ddanijell/ATU-Antenna-Tuner-System/Photo/ATU130_and_ATUdisplay.jpg

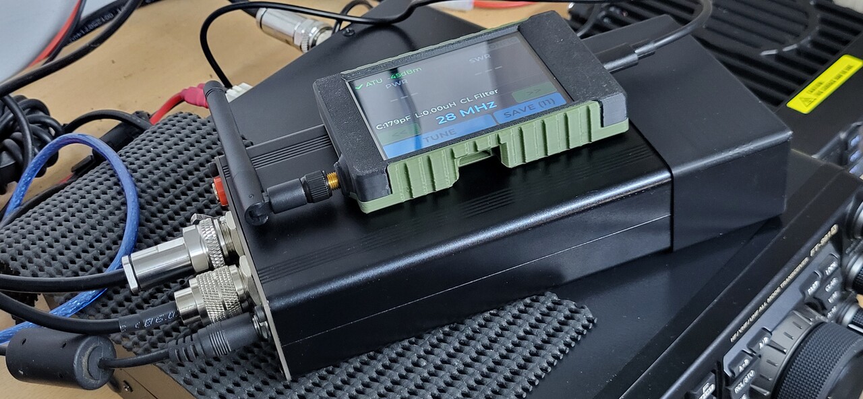
Photo/ATU130_and_ATUdisplay.jpg
