ddanijell/ATU-Antenna-Tuner-System/Photo/ATU130_front_cover.jpg

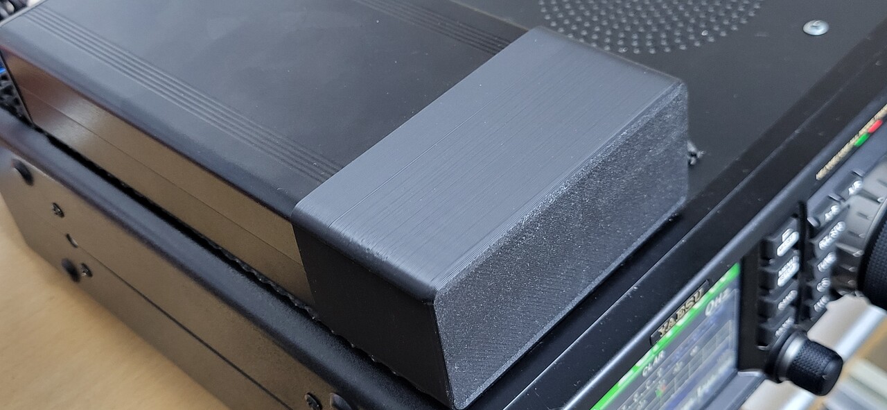
Photo/ATU130_front_cover.jpg
