ddanijell/ATU-Antenna-Tuner-System/Photo/ATU_transiver.jpg

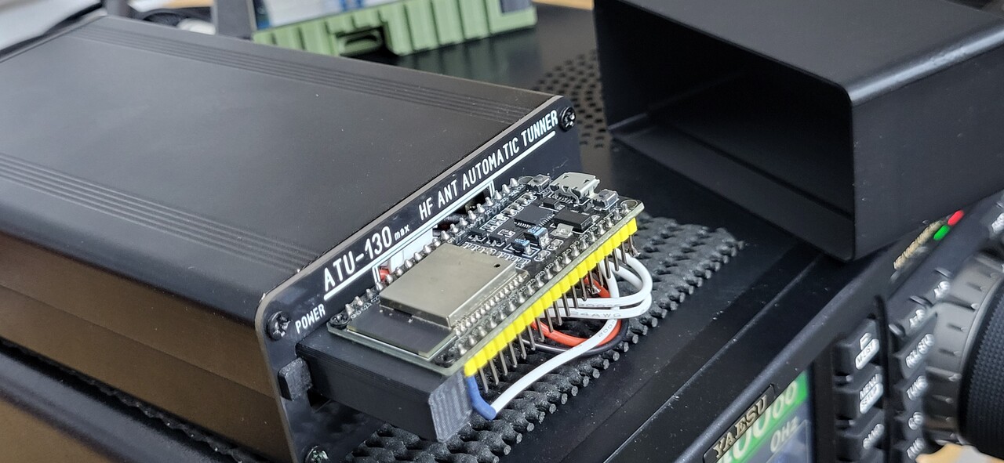
Photo/ATU_transiver.jpg
