ddanijell/ATU-Antenna-Tuner-System/Photo/ATUdisplay_back.jpg

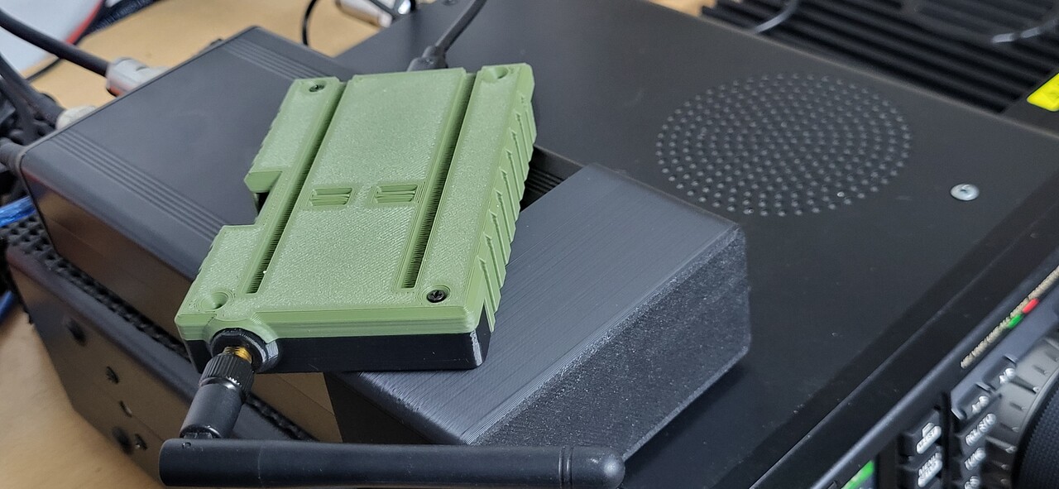
Photo/ATUdisplay_back.jpg
