ddanijell/ATU-Antenna-Tuner-System/Photo/Brightnes_Pair.jpg

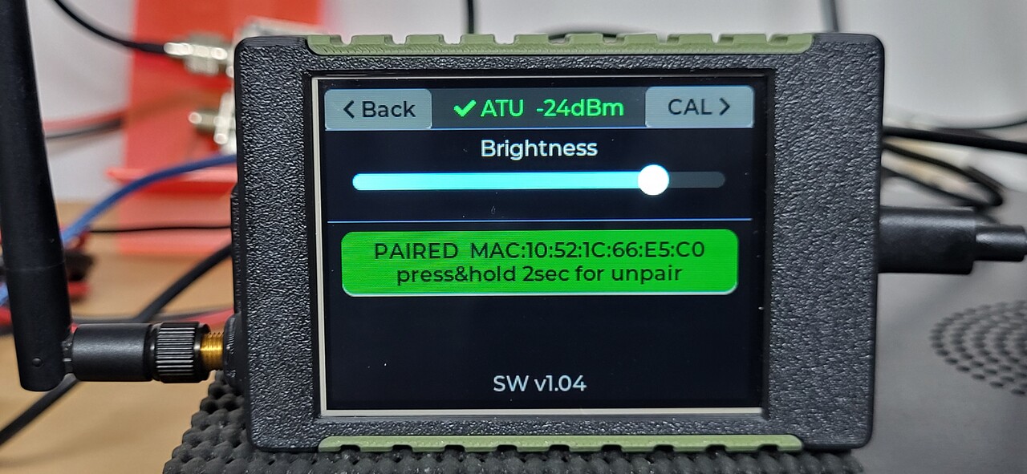
Photo/Brightnes_Pair.jpg
