ddanijell/ATU-Antenna-Tuner-System/Photo/CYD_ESP32_PCB.jpg

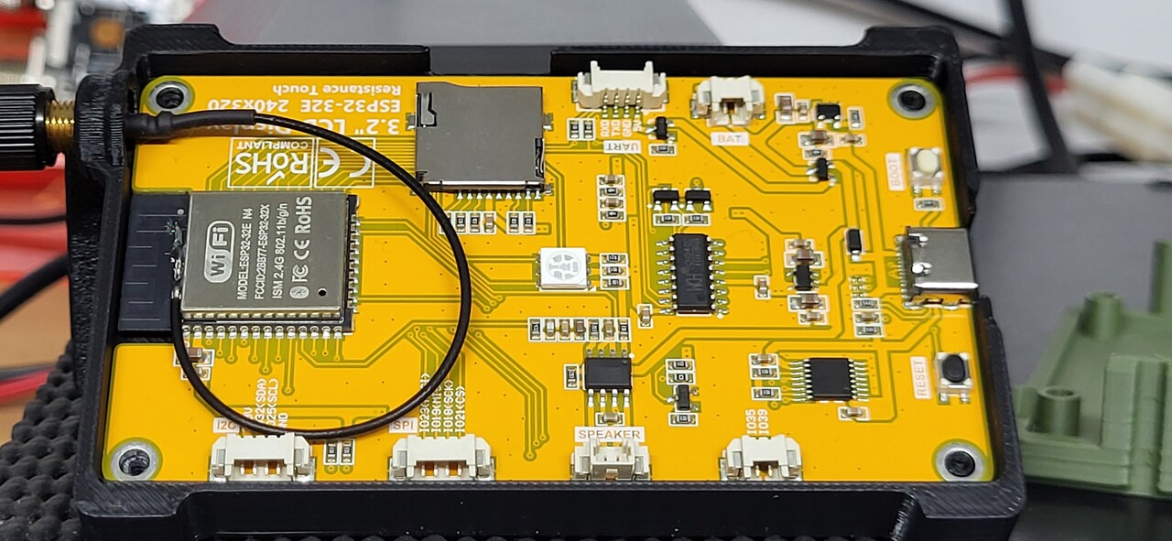
Photo/CYD_ESP32_PCB.jpg
