ddanijell/ATU-Antenna-Tuner-System/Photo/inside_atu130.jpg

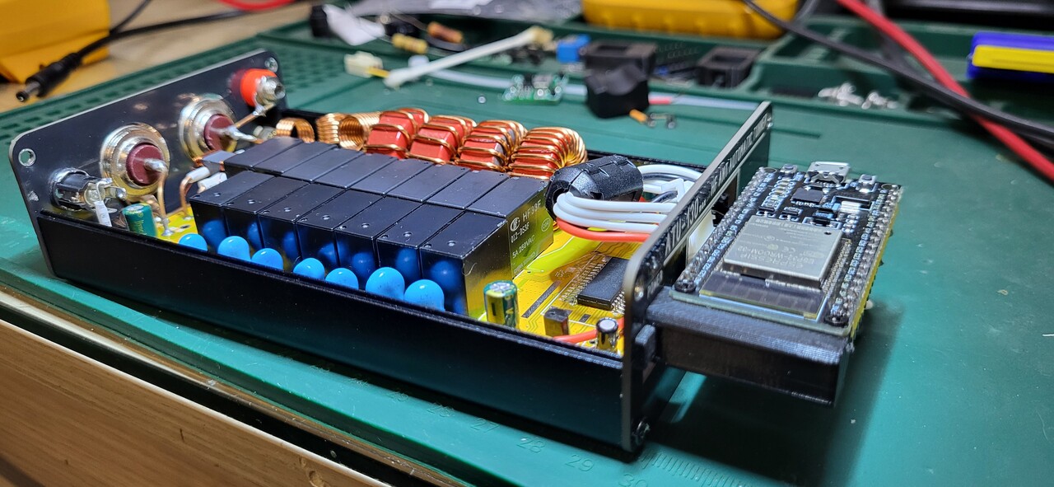
Photo/inside_atu130.jpg
