ddanijell/ATU-Antenna-Tuner-System/Photo/sideview.jpg

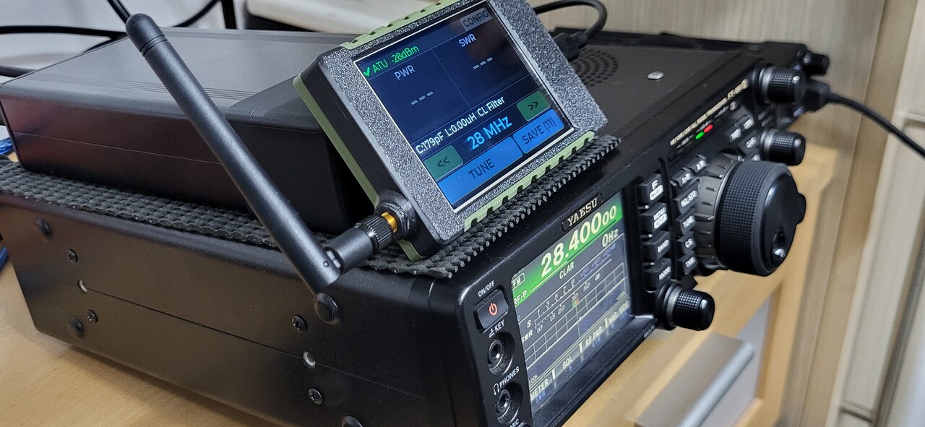
Photo/sideview.jpg
