ddanijell/ATU-Antenna-Tuner-System/Photo/system_01.jpg

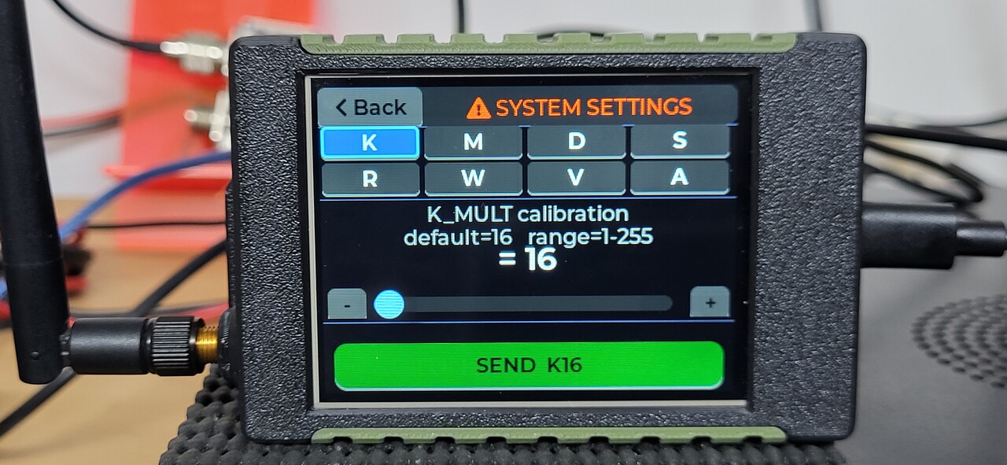
Photo/system_01.jpg
