ddanijell/ATU-Antenna-Tuner-System/Photo/system_06.jpg

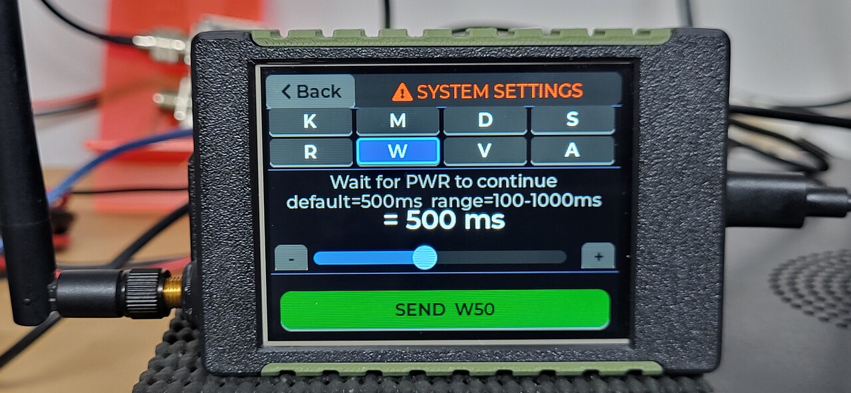
Photo/system_06.jpg
