ddanijell/ATU-Antenna-Tuner-System/Photo/system_08.jpg

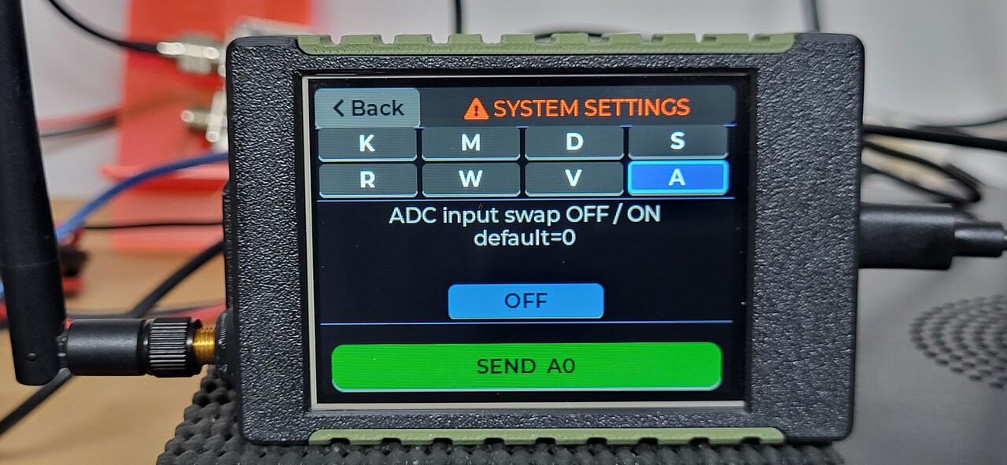
Photo/system_08.jpg
