ddanijell/ATU-Antenna-Tuner-System/Photo/Manual_L_C_tuning.jpg

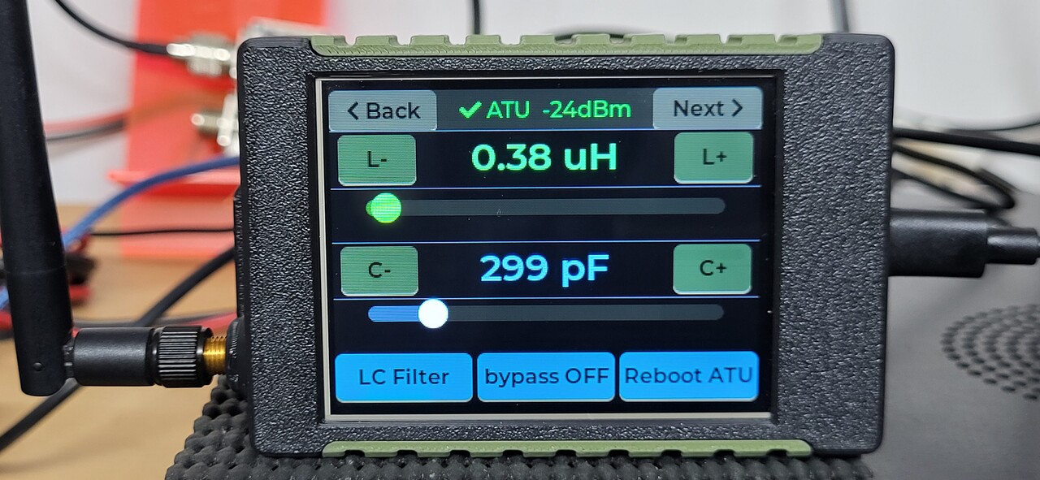
Photo/Manual_L_C_tuning.jpg
